Gallarfrox/WRO-FE-XPRIT-2024/Edge Impulse/images_of_Green Obstacle/Green Obstacle_1725329762552.jpg

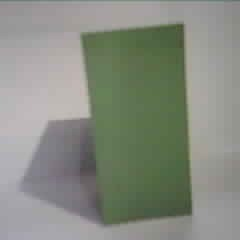
Edge Impulse/images_of_Green Obstacle/Green Obstacle_1725329762552.jpg
