Gallarfrox/WRO-FE-XPRIT-2024/Edge Impulse/images_of_Red Obstacle/Red Obstacle_1725329590040.jpg

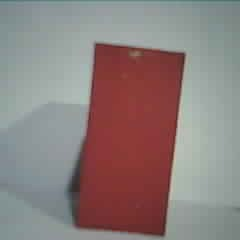
Edge Impulse/images_of_Red Obstacle/Red Obstacle_1725329590040.jpg
