Gallarfrox/WRO-FE-XPRIT-2024/Images/Risht_side_Robot.jpg

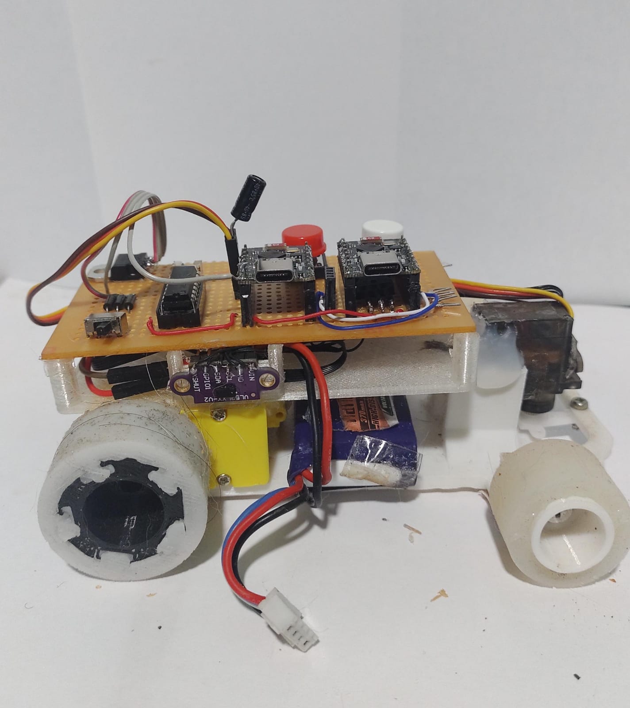
Images/Risht_side_Robot.jpg
